lostretrotapes/AT-Y-SPEC-MATE-Re-Creation/images/CORR_IMG_0024.jpg

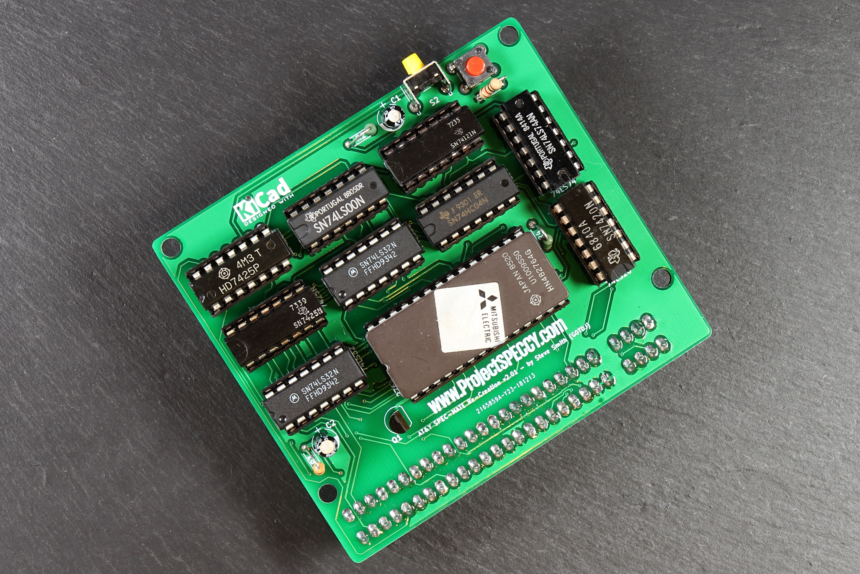
images/CORR_IMG_0024.jpg
