lostretrotapes/AT-Y-SPEC-MATE-Re-Creation/images/Spectrum Spec-Mate v2.01_Gerblook_Back.png

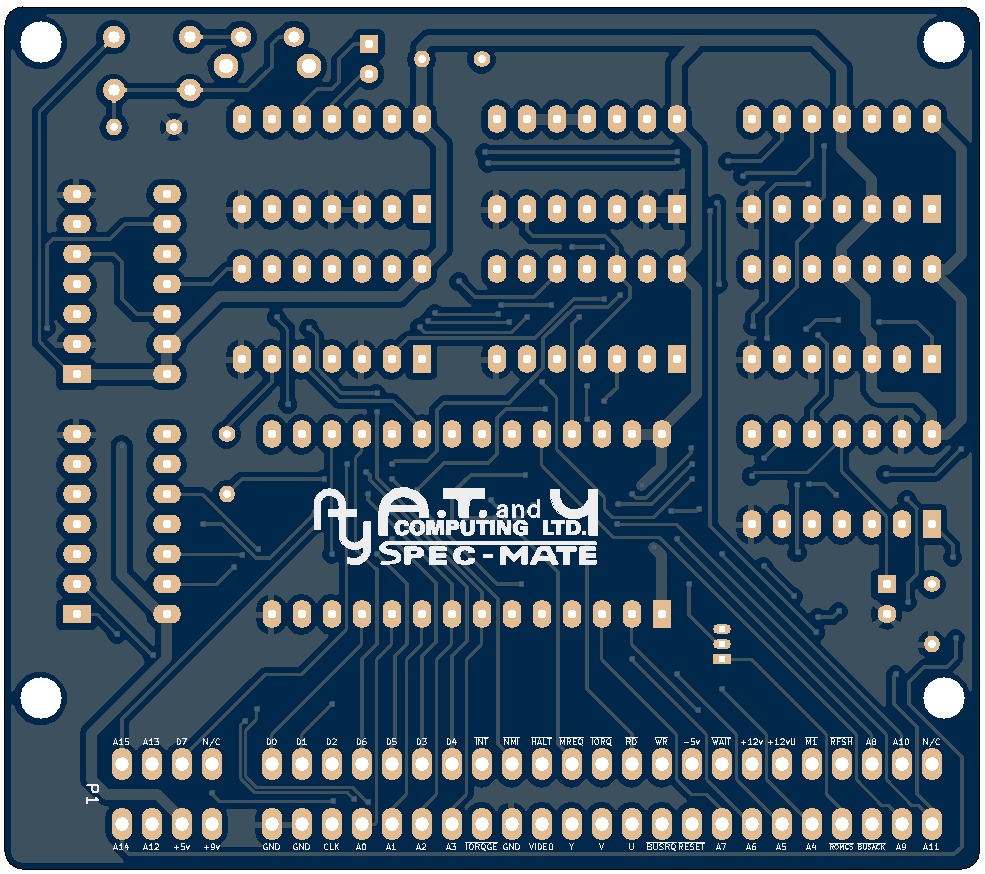
images/Spectrum Spec-Mate v2.01_Gerblook_Back.png
